GAPS-Collab/drs4-board/sim/cheb_7ord.asc

C1: cap; 150p; Rser=2
C2: cap; 270p; Rser=2
C3: cap; 270p; Rser=2
C4: cap; 150p; Rser=2
C5: cap; 1µ
L1: ind; 470n; Ipk=0.1 Rser=0.5
L2: ind; 510n; Ipk=0.1 Rser=0.5
L3: ind; 470n; Ipk=0.1 Rser=0.5
R1: res; 50
R2: res; 50
R3: res; 300
R4: res; 18
R5: res; 300
V1: voltage; PULSE(0 2.5 0 2n 2n 20n 40n 500); Rser=0 Cpar=0
Named nets: 0
.tran 0 1us 0 0.5ns
Si5330 output
50 Ohm load
Analog front end
